engrtanveerahmed/MPPT/auto cade design pics/a1.PNG

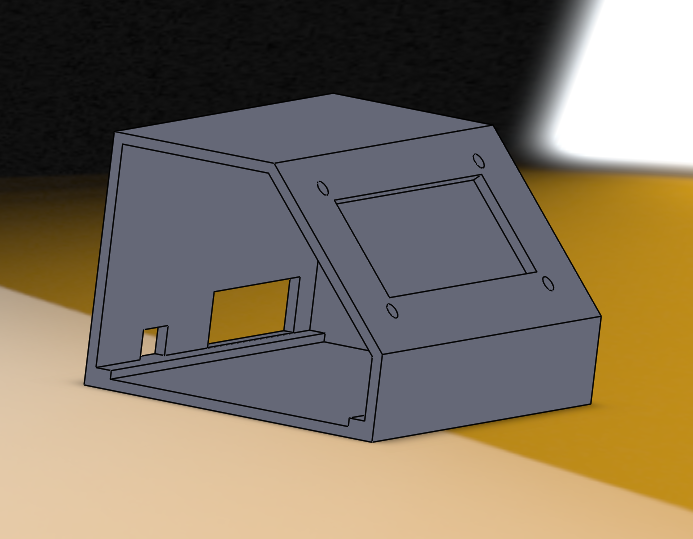
auto cade design pics/a1.PNG
