engrtanveerahmed/MPPT/auto cade design pics/a2.PNG

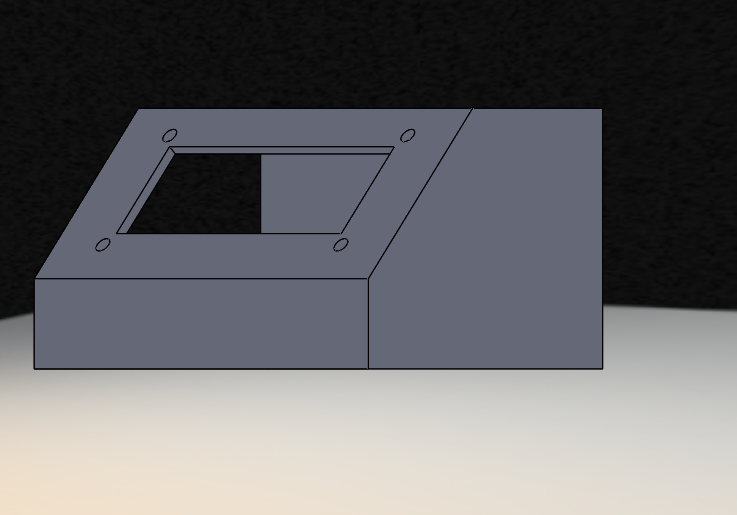
auto cade design pics/a2.PNG
