engrtanveerahmed/MPPT/auto cade design pics/bottom view.PNG

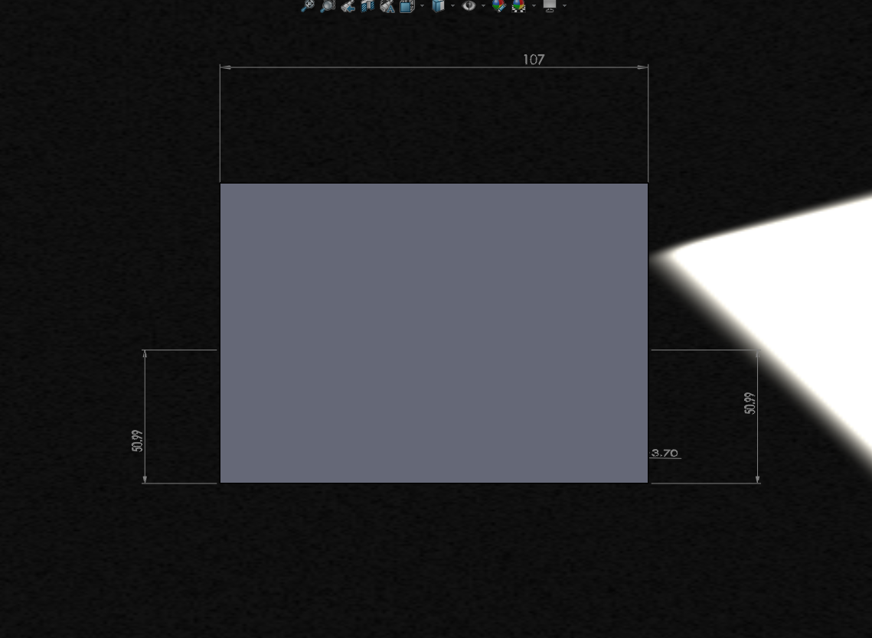
auto cade design pics/bottom view.PNG
