engrtanveerahmed/MPPT/auto cade design pics/mm2.PNG

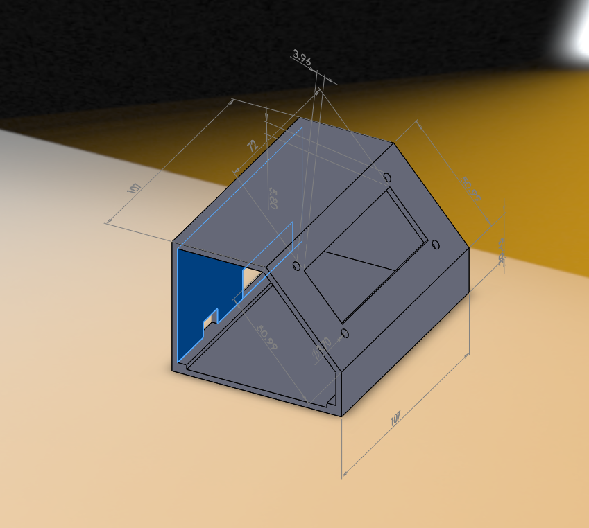
auto cade design pics/mm2.PNG
