engrtanveerahmed/MPPT/auto cade design pics/s1.PNG

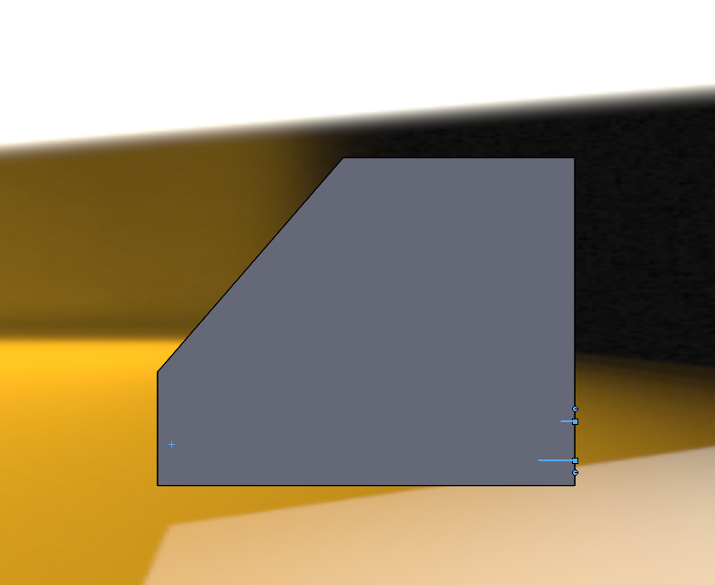
auto cade design pics/s1.PNG
