engrtanveerahmed/MPPT/pic of major component/Algorithm.jpg

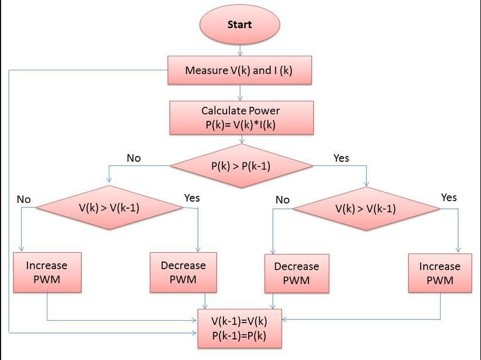
pic of major component/Algorithm.jpg
