engrtanveerahmed/MPPT/pic of major component/circut board.jpeg

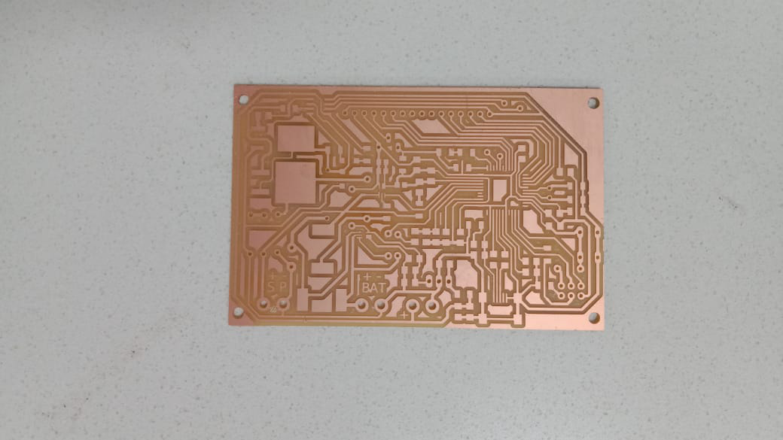
pic of major component/circut board.jpeg
