engrtanveerahmed/MPPT/pic of major component/full cirsuit (8).jpeg

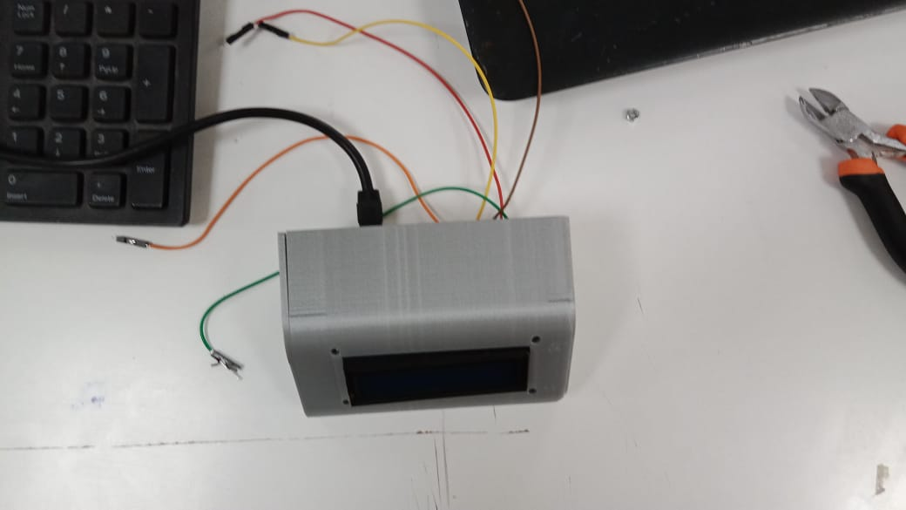
pic of major component/full cirsuit (8).jpeg
