engrtanveerahmed/MPPT/pic of major component/hbill of m.jpeg

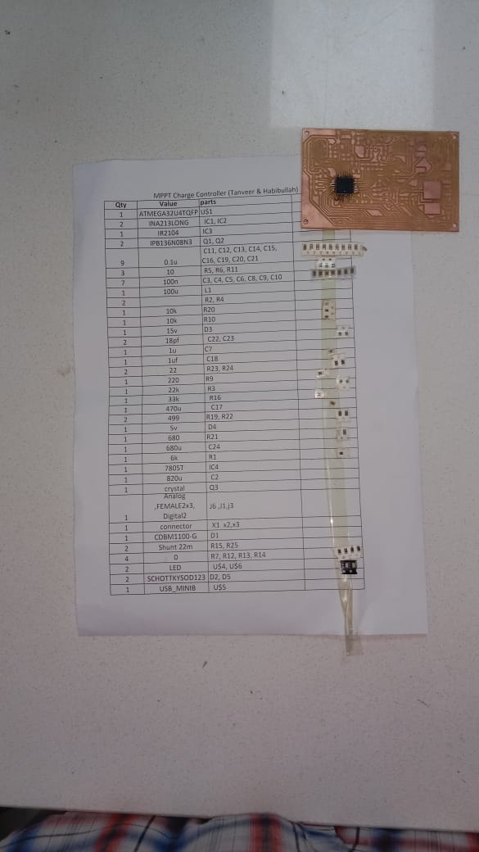
pic of major component/hbill of m.jpeg
