engrtanveerahmed/MPPT/pic of major component/ina213.jpg

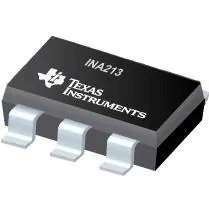
pic of major component/ina213.jpg
