engrtanveerahmed/MPPT/pic of major component/Picture1.png

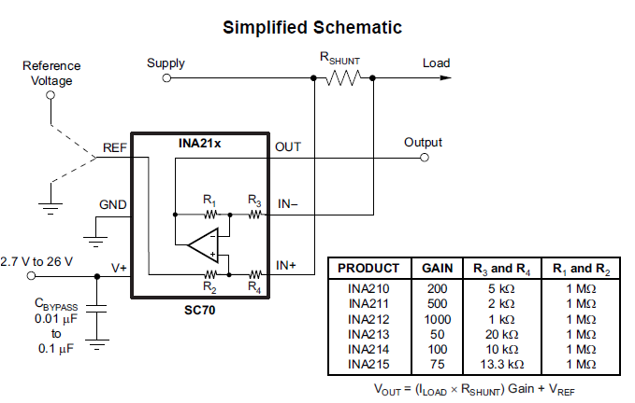
pic of major component/Picture1.png
