engrtanveerahmed/MPPT/pic of major component/tanveer.PNG

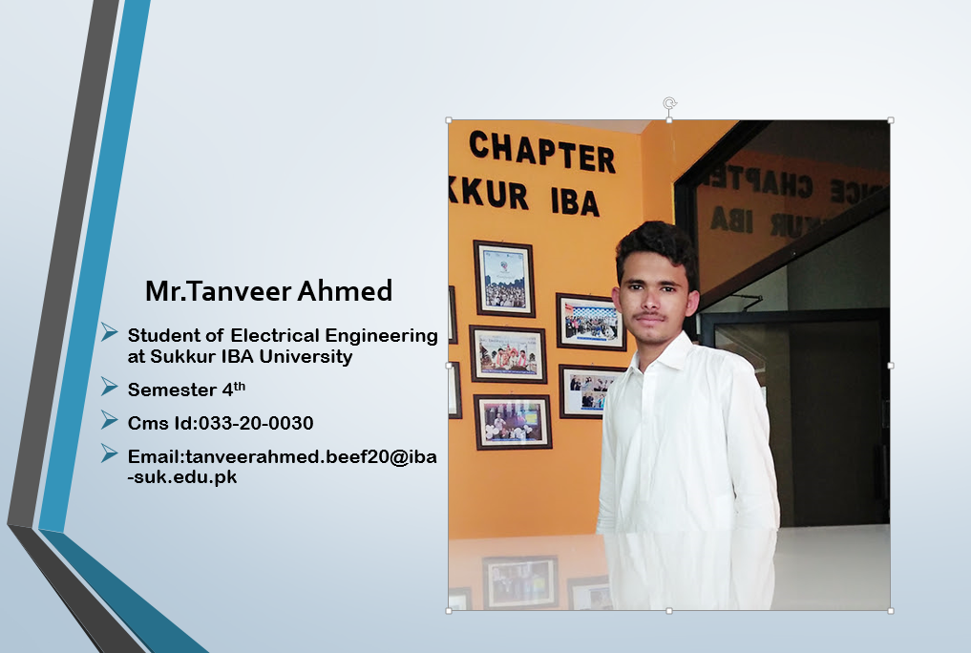
pic of major component/tanveer.PNG
