engrtanveerahmed/MPPT/pic of major component/w routing.jpeg

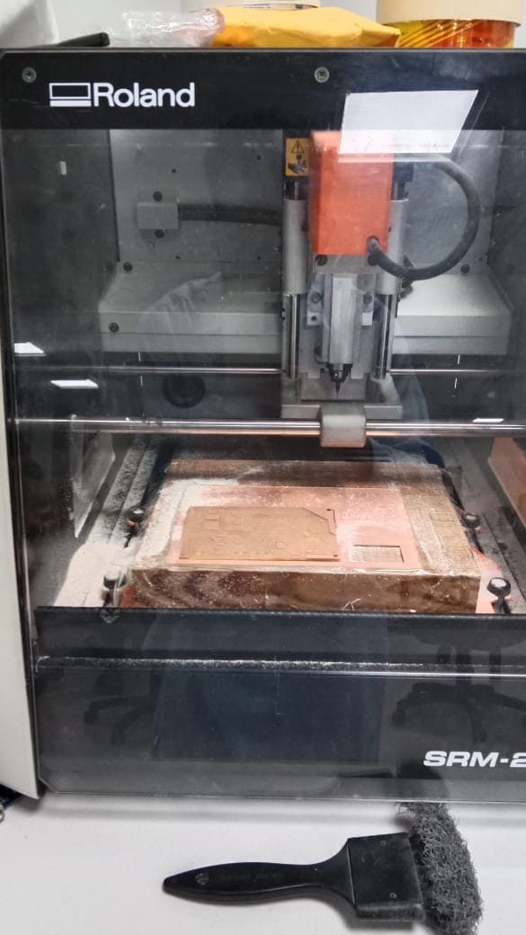
pic of major component/w routing.jpeg
